takehiro-code/CANnect/Sensor Components KiCAD/Sensor.sch

## KiCad design Sensor Components KiCAD/Sensor.sch (2020-11-01)

Schematic: Sensor.sch

Parts:
C1, C2: 100nF
C3: 4.7uF
C4: 0.1uF
C5: 1uF
C6: 22uF
L1: 4.7uH
R1, R2: 10kΩ
U1: LSM6DSLTR
U2: MAX25276ATCA_VY+
U3: ESP32_WROOM_32_DEV; ESP32-WROOM-32-DEV
